unspecworks/raii/pcb/raii020.kicad_sch

## KiCad design pcb/raii020.kicad_sch (2025-11-23)

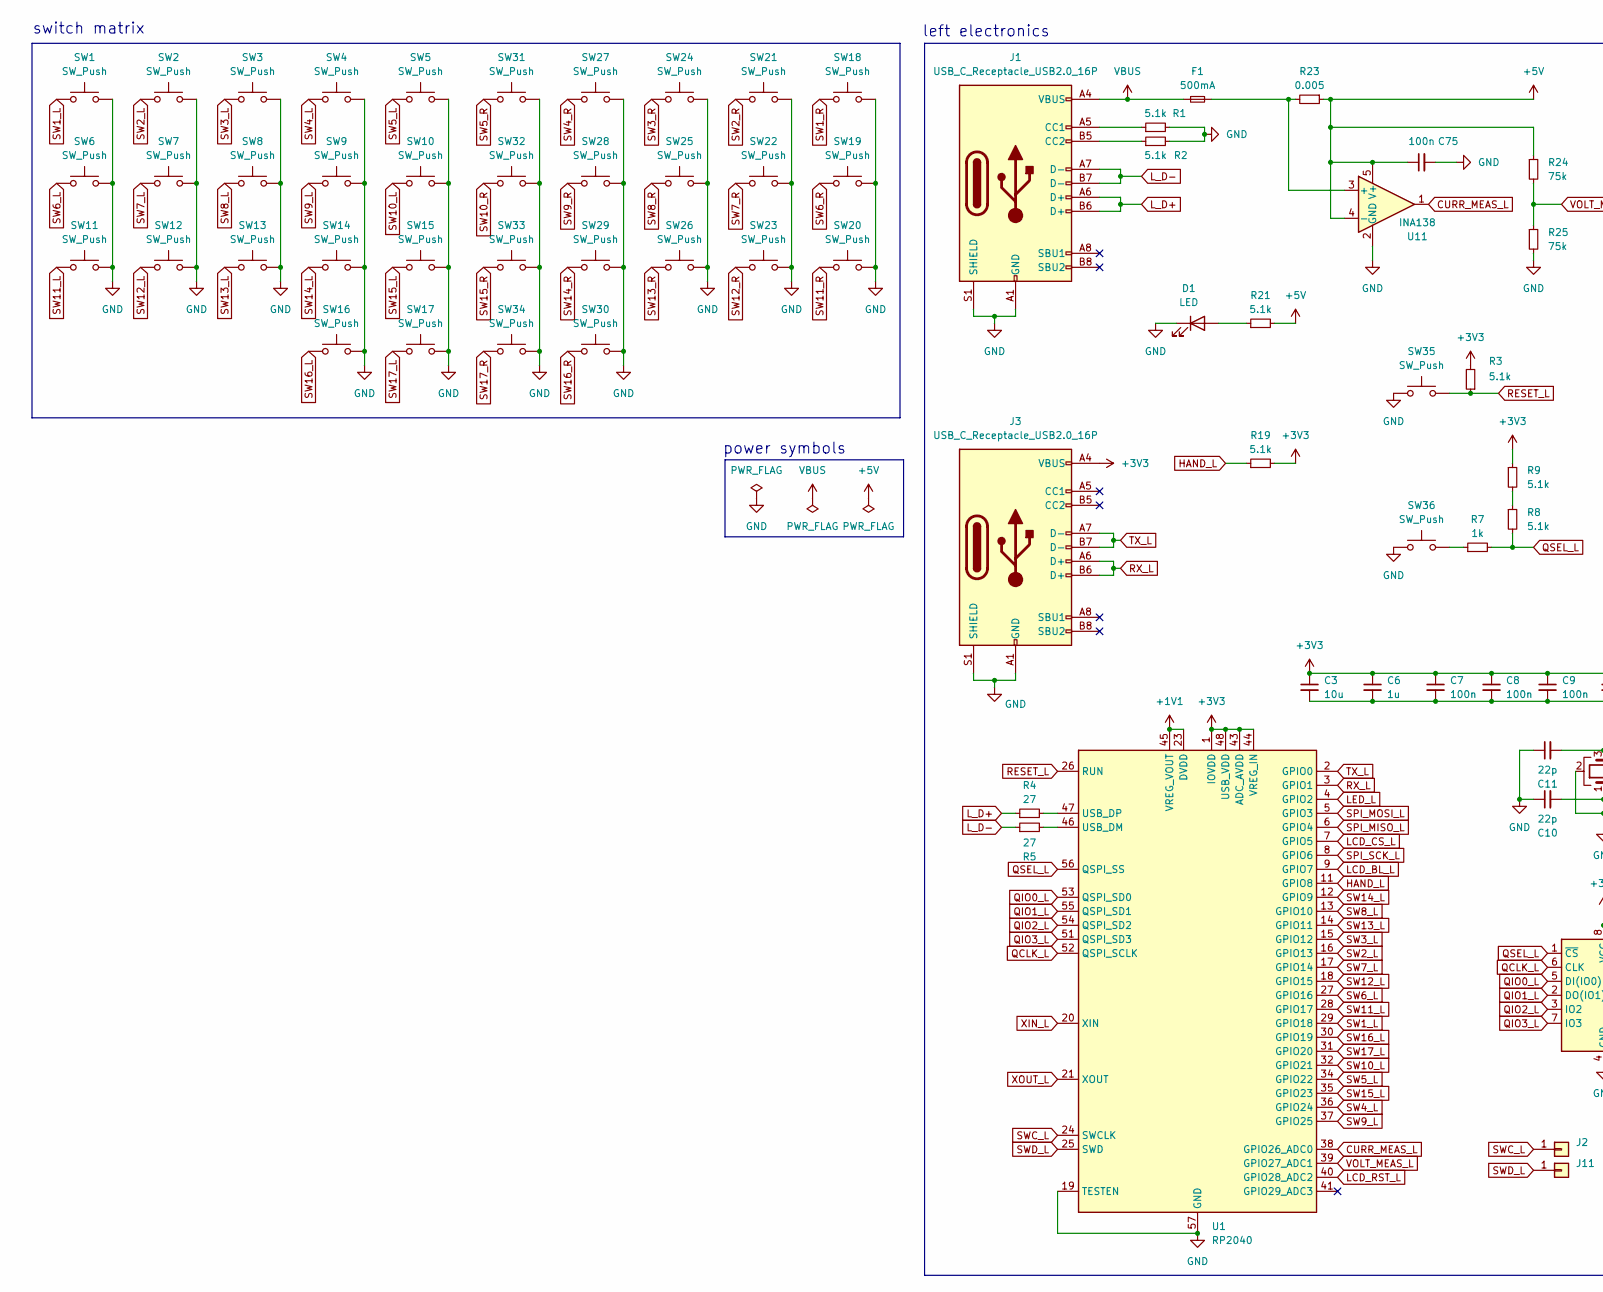
[picture p12: schematic raii020.kicad_sch, part in row 1, column 1]

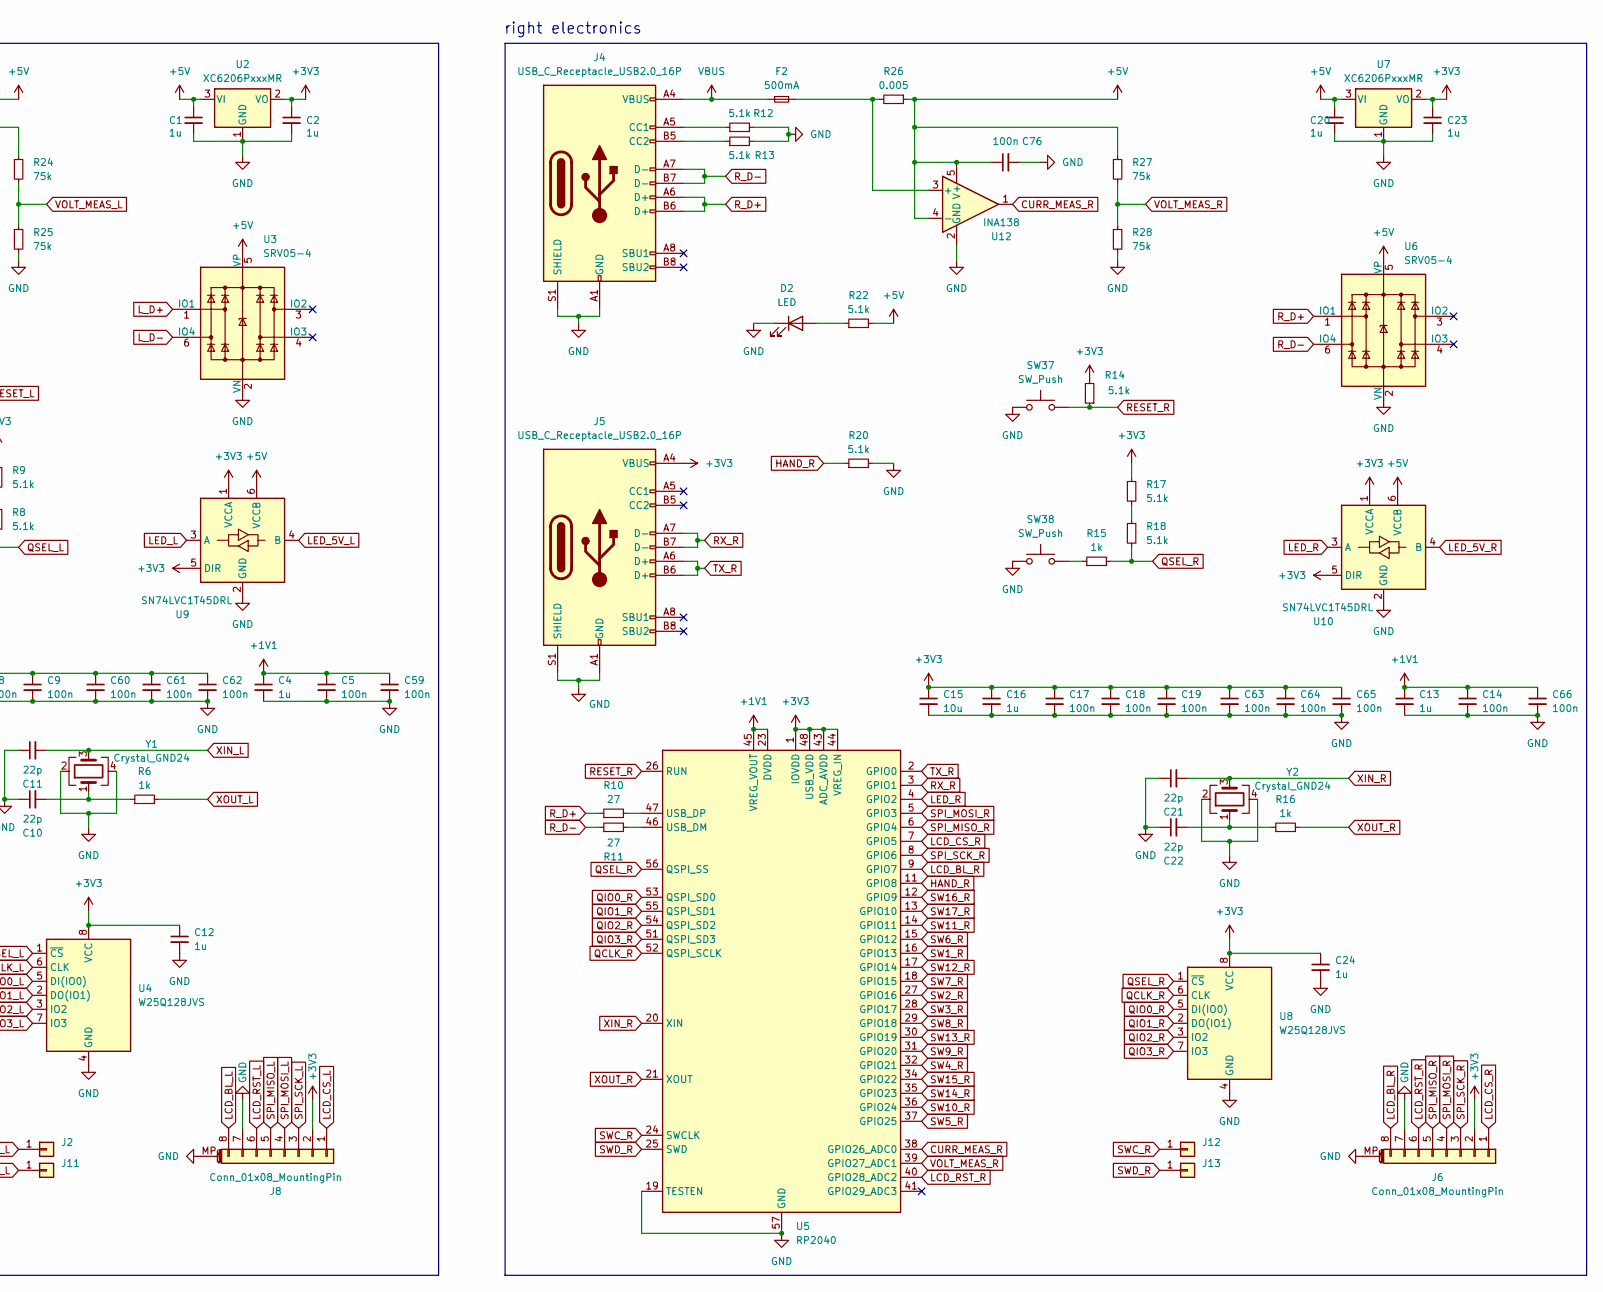
[picture p13: schematic raii020.kicad_sch, part in row 1, column 2]

Parts:
C1, C2, C4, C6, C12, C13, C16, C20, C23, C24: 1u; C_0402_1005Metric
C3, C15: 10u; C_0603_1608Metric
C5, C7, C8, C9, C14, C17, C18, C19, C59, C60, C61, C62, C63, C64, C65, C66, C75, C76: 100n; C_0402_1005Metric
C10, C11, C21, C22: 22p; C_0402_1005Metric
D1, D2: LED; LED_0603_1608Metric
F1, F2: 500mA; Fuse_1206_3216Metric
J1, J3, J4, J5: USB_C_Receptacle_USB2.0_16P; USB_C_Receptacle_HRO_TYPE-C-31-M-12
J2, J11, J12, J13: Conn_01x01; TestPoint_Pad_D1.0mm
J6, J8: Conn_01x08_MountingPin; TE_0-1734839-8_1x08-1MP_P0.5mm_Horizontal
R1, R2, R3, R8, R9, R12, R13, R14, R17, R18, R19, R20, R21, R22: 5.1k; R_0402_1005Metric
R4, R5, R10, R11: 27; R_0402_1005Metric
R6, R7, R15, R16: 1k; R_0402_1005Metric
R23, R26: 0.005; R_1206_3216Metric
R24, R25, R27, R28: 75k; R_0402_1005Metric
SW1, SW2, SW3, SW4, SW5, SW6, SW7, SW8, SW9, SW10, SW11, SW12, SW13, SW14, SW15, SW16, SW17, SW18, SW19, SW20, SW21, SW22, SW23, SW24, SW25, SW26, SW27, SW28, SW29, SW30, SW31, SW32, SW33, SW34: SW_Push; SW_choc_v1_1u
SW35, SW36, SW37, SW38: SW_Push; SW_SPST_B3U-1000P
U1, U5: RP2040; QFN-56-1EP_7x7mm_P0.4mm_EP3.2x3.2mm
U2, U7: XC6206PxxxMR; SOT-23-3
U3, U6: SRV05-4; SOT-23-6-routable
U4, U8: W25Q128JVS; SOIC-8_5.23x5.23mm_P1.27mm
U9, U10: SN74LVC1T45DRL; SOT-563
U11, U12: INA138; SOT-23-5
Y1, Y2: Crystal_GND24; Crystal_SMD_3225-4Pin_3.2x2.5mm

Connections:
+1V1: C4.1, C5.1, C13.1, C14.1, C59.1, C66.1, U1.23 (DVDD), U1.45 (VREG_VOUT), U1.50 (DVDD), U5.23 (DVDD), U5.45 (VREG_VOUT), U5.50 (DVDD)
+3V3: C2.1, C3.1, C6.1, C7.1, C8.1, C9.1, C12.1, C15.1, C16.1, C17.1, C18.1, C19.1, C23.1, C24.1, C60.1, C61.1, C62.1, C63.1, C64.1, C65.1, J3.A4 (VBUS), J3.A9 (VBUS), J3.B4 (VBUS), J3.B9 (VBUS), J5.A4 (VBUS), J5.A9 (VBUS), J5.B4 (VBUS), J5.B9 (VBUS), J6.2, J8.2, R3.2, R9.1, R14.2, R17.1, R19.2, U1.1 (IOVDD), U1.10 (IOVDD), U1.22 (IOVDD), U1.33 (IOVDD), U1.42 (IOVDD), U1.43 (ADC_AVDD), U1.44 (VREG_IN), U1.48 (USB_VDD), U1.49 (IOVDD), U2.2 (VO), U4.8 (VCC), U5.1 (IOVDD), U5.10 (IOVDD), U5.22 (IOVDD), U5.33 (IOVDD), U5.42 (IOVDD), U5.43 (ADC_AVDD), U5.44 (VREG_IN), U5.48 (USB_VDD), U5.49 (IOVDD), U7.2 (VO), U8.8 (VCC), U9.1 (VCCA), U9.5 (DIR), U10.1 (VCCA), U10.5 (DIR)
+5V: C1.1, C20.1, C75.1, C76.1, R21.2, R22.2, R23.1, R24.1, R26.1, R27.1, U2.3 (VI), U3.5 (VP), U6.5 (VP), U7.3 (VI), U9.6 (VCCB), U10.6 (VCCB), U11.4 (-), U11.5 (V+), U12.4 (-), U12.5 (V+)
CURR_MEAS_L: U1.38 (GPIO26_ADC0), U11.1
CURR_MEAS_R: U5.38 (GPIO26_ADC0), U12.1
GND: C1.2, C2.2, C3.2, C4.2, C5.2, C6.2, C7.2, C8.2, C9.2, C10.1, C11.1, C12.2, C13.2, C14.2, C15.2, C16.2, C17.2, C18.2, C19.2, C20.2, C21.1, C22.1, C23.2, C24.2, C59.2, C60.2, C61.2, C62.2, C63.2, C64.2, C65.2, C66.2, C75.2, C76.2, D1.1 (K), D2.1 (K), J1.A1 (GND), J1.A12 (GND), J1.B1 (GND), J1.B12 (GND), J1.S1 (SHIELD), J3.A1 (GND), J3.A12 (GND), J3.B1 (GND), J3.B12 (GND), J3.S1 (SHIELD), J4.A1 (GND), J4.A12 (GND), J4.B1 (GND), J4.B12 (GND), J4.S1 (SHIELD), J5.A1 (GND), J5.A12 (GND), J5.B1 (GND), J5.B12 (GND), J5.S1 (SHIELD), J6.7, J6.MP (MountPin), J8.7, J8.MP (MountPin), R1.2, R2.2, R12.2, R13.2, R20.2, R25.2, R28.2, SW1.2, SW2.2, SW3.2, SW4.2, SW5.2, SW6.2, SW7.2, SW8.2, SW9.2, SW10.2, SW11.2, SW12.2, SW13.2, SW14.2, SW15.2, SW16.2, SW17.2, SW18.1, SW19.1, SW20.1, SW21.1, SW22.1, SW23.1, SW24.1, SW25.1, SW26.1, SW27.1, SW28.1, SW29.1, SW30.1, SW31.1, SW32.1, SW33.1, SW34.1, SW35.1, SW36.1, SW37.1, SW38.1, U1.19 (TESTEN), U1.57 (GND), U2.1 (GND), U3.2 (VN), U4.4 (GND), U5.19 (TESTEN), U5.57 (GND), U6.2 (VN), U7.1 (GND), U8.4 (GND), U9.2 (GND), U10.2 (GND), U11.2 (GND), U12.2 (GND), Y1.2, Y1.4, Y2.2, Y2.4
HAND_L: R19.1, U1.11 (GPIO8)
HAND_R: R20.1, U5.11 (GPIO8)
LCD_BL_L: J8.8, U1.9 (GPIO7)
LCD_BL_R: J6.8, U5.9 (GPIO7)
LCD_CS_L: J8.1, U1.7 (GPIO5)
LCD_CS_R: J6.1, U5.7 (GPIO5)
LCD_RST_L: J8.6, U1.40 (GPIO28_ADC2)
LCD_RST_R: J6.6, U5.40 (GPIO28_ADC2)
LED_5V_L: U9.4 (B)
LED_5V_R: U10.4 (B)
LED_L: U1.4 (GPIO2), U9.3 (A)
LED_R: U5.4 (GPIO2), U10.3 (A)
L_D+: J1.A6 (D+), J1.B6 (D+), R4.1, U3.1 (IO1)
L_D-: J1.A7 (D-), J1.B7 (D-), R5.1, U3.6 (IO4)
unnamed: C10.2, R6.1, Y1.1
unnamed: C22.2, R16.1, Y2.1
unnamed: D1.2 (A), R21.1
unnamed: D2.2 (A), R22.1
unnamed: F1.2, R23.2, U11.3 (+)
unnamed: F2.2, R26.2, U12.3 (+)
unnamed: J1.A5 (CC1), R1.1
unnamed: J1.B5 (CC2), R2.1
unnamed: J4.A5 (CC1), R12.1
unnamed: J4.B5 (CC2), R13.1
unnamed: R4.2, U1.47 (USB_DP)
unnamed: R5.2, U1.46 (USB_DM)
unnamed: R7.1, SW36.2
unnamed: R8.1, R9.2
unnamed: R10.2, U5.47 (USB_DP)
unnamed: R11.2, U5.46 (USB_DM)
unnamed: R15.1, SW38.2
unnamed: R17.2, R18.1
QCLK_L: U1.52 (QSPI_SCLK), U4.6 (CLK)
QCLK_R: U5.52 (QSPI_SCLK), U8.6 (CLK)
QIO0_L: U1.53 (QSPI_SD0), U4.5 (DI(IO0))
QIO0_R: U5.53 (QSPI_SD0), U8.5 (DI(IO0))
QIO1_L: U1.55 (QSPI_SD1), U4.2 (DO(IO1))
QIO1_R: U5.55 (QSPI_SD1), U8.2 (DO(IO1))
QIO2_L: U1.54 (QSPI_SD2), U4.3 (IO2)
QIO2_R: U5.54 (QSPI_SD2), U8.3 (IO2)
QIO3_L: U1.51 (QSPI_SD3), U4.7 (IO3)
QIO3_R: U5.51 (QSPI_SD3), U8.7 (IO3)
QSEL_L: R7.2, R8.2, U1.56 (QSPI_SS), U4.1 (~CS)
QSEL_R: R15.2, R18.2, U5.56 (QSPI_SS), U8.1 (~CS)
RESET_L: R3.1, SW35.2, U1.26 (RUN)
RESET_R: R14.1, SW37.2, U5.26 (RUN)
RX_L: J3.A6 (D+), J3.B6 (D+), U1.3 (GPIO1)
RX_R: J5.A7 (D-), J5.B7 (D-), U5.3 (GPIO1)
R_D+: J4.A6 (D+), J4.B6 (D+), R10.1, U6.1 (IO1)
R_D-: J4.A7 (D-), J4.B7 (D-), R11.1, U6.6 (IO4)
SPI_MISO_L: J8.5, U1.6 (GPIO4)
SPI_MISO_R: J6.5, U5.6 (GPIO4)
SPI_MOSI_L: J8.4, U1.5 (GPIO3)
SPI_MOSI_R: J6.4, U5.5 (GPIO3)
SPI_SCK_L: J8.3, U1.8 (GPIO6)
SPI_SCK_R: J6.3, U5.8 (GPIO6)
SW1_L: SW1.1, U1.29 (GPIO18)
SW1_R: SW18.2, U5.16 (GPIO13)
SW2_L: SW2.1, U1.16 (GPIO13)
SW2_R: SW21.2, U5.27 (GPIO16)
SW3_L: SW3.1, U1.15 (GPIO12)
SW3_R: SW24.2, U5.28 (GPIO17)
SW4_L: SW4.1, U1.36 (GPIO24)
SW4_R: SW27.2, U5.32 (GPIO21)
SW5_L: SW5.1, U1.34 (GPIO22)
SW5_R: SW31.2, U5.37 (GPIO25)
SW6_L: SW6.1, U1.27 (GPIO16)
SW6_R: SW19.2, U5.15 (GPIO12)
SW7_L: SW7.1, U1.17 (GPIO14)
SW7_R: SW22.2, U5.18 (GPIO15)
SW8_L: SW8.1, U1.13 (GPIO10)
SW8_R: SW25.2, U5.29 (GPIO18)
SW9_L: SW9.1, U1.37 (GPIO25)
SW9_R: SW28.2, U5.31 (GPIO20)
SW10_L: SW10.1, U1.32 (GPIO21)
SW10_R: SW32.2, U5.36 (GPIO24)
SW11_L: SW11.1, U1.28 (GPIO17)
SW11_R: SW20.2, U5.14 (GPIO11)
SW12_L: SW12.1, U1.18 (GPIO15)
SW12_R: SW23.2, U5.17 (GPIO14)
SW13_L: SW13.1, U1.14 (GPIO11)
SW13_R: SW26.2, U5.30 (GPIO19)
SW14_L: SW14.1, U1.12 (GPIO9)
SW14_R: SW29.2, U5.35 (GPIO23)
SW15_L: SW15.1, U1.35 (GPIO23)
SW15_R: SW33.2, U5.34 (GPIO22)
SW16_L: SW16.1, U1.30 (GPIO19)
SW16_R: SW30.2, U5.12 (GPIO9)
SW17_L: SW17.1, U1.31 (GPIO20)
SW17_R: SW34.2, U5.13 (GPIO10)
SWC_L: J2.1, U1.24 (SWCLK)
SWC_R: J12.1, U5.24 (SWCLK)
SWD_L: J11.1, U1.25 (SWD)
SWD_R: J13.1, U5.25 (SWD)
TX_L: J3.A7 (D-), J3.B7 (D-), U1.2 (GPIO0)
TX_R: J5.A6 (D+), J5.B6 (D+), U5.2 (GPIO0)
VBUS: F1.1, F2.1, J1.A4 (VBUS), J1.A9 (VBUS), J1.B4 (VBUS), J1.B9 (VBUS), J4.A4 (VBUS), J4.A9 (VBUS), J4.B4 (VBUS), J4.B9 (VBUS)
VOLT_MEAS_L: R24.2, R25.1, U1.39 (GPIO27_ADC1)
VOLT_MEAS_R: R27.2, R28.1, U5.39 (GPIO27_ADC1)
XIN_L: C11.2, U1.20 (XIN), Y1.3
XIN_R: C21.2, U5.20 (XIN), Y2.3
XOUT_L: R6.2, U1.21 (XOUT)
XOUT_R: R16.2, U5.21 (XOUT)

Notes on the sheet:
switch matrix
left electronics
power symbols
right electronics
